Noxet/LEDROCK/firmware/src/http_server.cpp

#include "http_server.h"
#include "freertos/projdefs.h"
#include "message.h"

#include <esp_wifi.h>
#include <esp_event.h>
#include <esp_log.h>
#include <esp_system.h>
#include <nvs_flash.h>
#include <sys/param.h>
#include "core/log.h"
#include "esp_netif.h"
#include "esp_eth.h"
#include "esp_timer.h"
#include "freertos/idf_additions.h"
#include "portmacro.h"
#include "protocol_examples_common.h"
#include "protocol_examples_utils.h"

#include <esp_http_server.h>
#include <vector>
#include <string>


static void disconnect_handler(void* arg, esp_event_base_t event_base, int32_t event_id, void* event_data);
static void connect_handler(void* arg, esp_event_base_t event_base, int32_t event_id, void* event_data);
static esp_err_t startPageHandler(httpd_req_t *req);
static esp_err_t ws_handler(httpd_req_t *req);
static std::vector<std::string> splitPayload(char *msg);
static MsgType parseMsgType(std::string &s);


// Embedded zipped html file
extern const uint8_t index_html_gz_start[] asm("_binary_index_html_gz_start");
extern const uint8_t index_html_gz_end[] asm("_binary_index_html_gz_end");
static size_t index_html_gz_len = index_html_gz_end - index_html_gz_start;

#define MAX_CLIENT_FAILED 5

struct client
{
    int fd;
    int failedAttempts;
};

static std::vector<struct client> g_clients;

/* A simple example that demonstrates using websocket echo server
 */
static const char *TAG = "ws_echo_server";

/*
 * Structure holding server handle
 * and internal socket fd in order
 * to use out of request send
 */
struct async_resp_arg {
    httpd_handle_t hd;
    int fd;
};


HTTPServer::HTTPServer(QueueHandle_t lcQueue)
    : m_lcQueue(lcQueue)
{
    m_httpQueue = xQueueCreate(20, sizeof(char *));
}


void HTTPServer::init()
{
    ESP_ERROR_CHECK(nvs_flash_init());
    ESP_ERROR_CHECK(esp_netif_init());
    ESP_ERROR_CHECK(esp_event_loop_create_default());

    /* This helper function configures Wi-Fi or Ethernet, as selected in menuconfig.
     * Read "Establishing Wi-Fi or Ethernet Connection" section in
     * examples/protocols/README.md for more information about this function.
     */
    ESP_ERROR_CHECK(example_connect());

    /* Register event handlers to stop the server when Wi-Fi or Ethernet is disconnected,
     * and re-start it upon connection.
     */
    ESP_ERROR_CHECK(esp_event_handler_register(IP_EVENT, IP_EVENT_STA_GOT_IP, &connect_handler, this));
    ESP_ERROR_CHECK(esp_event_handler_register(WIFI_EVENT, WIFI_EVENT_STA_DISCONNECTED, &disconnect_handler, this));

    /* Start the server for the first time */
    startWebserver();
}


void HTTPServer::run()
{
    // TODO(noxet): free ptr?
    char *msg = nullptr;
    while(1)
    {
        // Blocking call, wait for message to log
        xQueueReceive(m_httpQueue, &msg, portMAX_DELAY);
        httpd_ws_frame_t ws_pkt;
        memset(&ws_pkt, 0, sizeof(httpd_ws_frame_t));
        ws_pkt.type = HTTPD_WS_TYPE_TEXT;
        ws_pkt.len = strlen(msg);
        ws_pkt.payload = (uint8_t *) msg;

        for (auto it = g_clients.begin(); it != g_clients.end();)
        {
            // TODO(noxet): Send sync instead?
            int ret = httpd_ws_send_frame_async(m_server, it->fd, &ws_pkt);
            if (ret != ESP_OK)
            {
                ESP_LOGI(TAG, "Failed to send log to client fd: %d", it->fd);
                it->failedAttempts++;
            }

            if (it->failedAttempts >= MAX_CLIENT_FAILED)
            {
                // Client probably disconnected, remove them from the list
                it = g_clients.erase(it);
            }
            else
            {
                ++it;
            }
        }
        vTaskDelay(500);
    }
}


httpd_handle_t HTTPServer::getServer()
{
    return m_server;
}


QueueHandle_t HTTPServer::getQueue()
{
    return m_httpQueue;
}


bool HTTPServer::queueLCEvent(Event &e)
{
    return xQueueSend(m_lcQueue, &e, 10);
}


void HTTPServer::startWebserver(void)
{
    const httpd_uri_t ws = {
        .uri        = "/ws",
        .method     = HTTP_GET,
        .handler    = ws_handler,
        .user_ctx   = this,
        .is_websocket = true,
        .handle_ws_control_frames = false,
        .supported_subprotocol = nullptr,
    };

    const httpd_uri_t startPage = {
        .uri = "/",
        .method = HTTP_GET,
        .handler = startPageHandler,
        .user_ctx = nullptr,
        .is_websocket = false,
        .handle_ws_control_frames = false,
        .supported_subprotocol = nullptr,
    };

    httpd_config_t config = HTTPD_DEFAULT_CONFIG();

    // Start the httpd server
    ESP_LOGI(TAG, "Starting server on port: '%d'", config.server_port);
    if (httpd_start(&m_server, &config) == ESP_OK) {
        // Registering the ws handler
        ESP_LOGI(TAG, "Registering URI handlers");
        httpd_register_uri_handler(m_server, &ws);
        httpd_register_uri_handler(m_server, &startPage);
    }

    ESP_LOGI(TAG, "Error starting server!");
}


void HTTPServer::stopWebserver()
{
    if (!m_server) return;

    esp_err_t res = httpd_stop(m_server);
    if (res == ESP_OK)
    {
        LRLOGI("HTTP Server stopped");
    }
    else
    {
        LRLOGI("Failed to stop HTTP Server");
    }
}


/*
 * async send function, which we put into the httpd work queue
 */
static void ws_async_send(void *arg)
{
    static const char * data = "Async data";
    struct async_resp_arg *resp_arg = static_cast<struct async_resp_arg *>(arg);
    httpd_handle_t hd = resp_arg->hd;
    int fd = resp_arg->fd;
    httpd_ws_frame_t ws_pkt;
    memset(&ws_pkt, 0, sizeof(httpd_ws_frame_t));
    ws_pkt.payload = (uint8_t*)data;
    ws_pkt.len = strlen(data);
    ws_pkt.type = HTTPD_WS_TYPE_TEXT;

    httpd_ws_send_frame_async(hd, fd, &ws_pkt);
    free(resp_arg);
}

static esp_err_t trigger_async_send(httpd_handle_t handle, httpd_req_t *req)
{
    struct async_resp_arg *resp_arg = static_cast<struct async_resp_arg *>(malloc(sizeof(struct async_resp_arg)));
    if (resp_arg == NULL) {
        return ESP_ERR_NO_MEM;
    }
    resp_arg->hd = req->handle;
    resp_arg->fd = httpd_req_to_sockfd(req);
    esp_err_t ret = httpd_queue_work(handle, ws_async_send, resp_arg);
    if (ret != ESP_OK) {
        free(resp_arg);
    }
    return ret;
}

static esp_err_t startPageHandler(httpd_req_t *req)
{
    if (req->method == HTTP_GET)
    {
        ESP_LOGI(TAG, "Got GET req");
    }

    char *buf;
    size_t bufLen = httpd_req_get_hdr_value_len(req, "Host") + 1;
    if (bufLen > 1)
    {
        buf = (char *) malloc(bufLen);
        assert(buf);
        ESP_LOGI(TAG, "Allocated %zu bytes for header", bufLen);
        if (httpd_req_get_hdr_value_str(req, "Host", buf, bufLen) == ESP_OK)
        {
            ESP_LOGI(TAG, "Got header -> Host: %s", buf);
        }
        free(buf);
    }

    bufLen = httpd_req_get_url_query_len(req) + 1;
    char decParam[1024]{};
    if (bufLen > 0)
    {
        buf = (char *) malloc(bufLen);
        assert(buf);
        if (httpd_req_get_url_query_str(req, buf, bufLen) == ESP_OK)
        {
            char param[1024];

            if (httpd_query_key_value(buf, "msg", param, sizeof(param)) == ESP_OK)
            {
                ESP_LOGI(TAG, "Got query -> msg: %s", param);
                example_uri_decode(decParam, param, strnlen(param, 1024));
                ESP_LOGI(TAG, "Decoded -> msg: %s", decParam);
            }
        }
        free(buf);
    }

    httpd_resp_set_type(req, "text/html");
    httpd_resp_set_hdr(req, "Content-Encoding", "gzip");

    httpd_resp_send(req, (const char *) index_html_gz_start, index_html_gz_len);

    return ESP_OK;
}

/*
 * This handler echos back the received ws data
 * and triggers an async send if certain message received
 */
static esp_err_t ws_handler(httpd_req_t *req)
{
    HTTPServer *httpServer = static_cast<HTTPServer *>(req->user_ctx);

    if (req->method == HTTP_GET) {
        int client_fd = httpd_req_to_sockfd(req);
        g_clients.push_back({.fd = client_fd, .failedAttempts = 0});
        ESP_LOGI(TAG, "Handshake done, the new connection was opened");
        return ESP_OK;
    }
    ESP_LOGI(TAG, "request method: %d", req->method);
    httpd_ws_frame_t ws_pkt;
    uint8_t *buf = NULL;
    memset(&ws_pkt, 0, sizeof(httpd_ws_frame_t));
    ws_pkt.type = HTTPD_WS_TYPE_TEXT;
    /* Set max_len = 0 to get the frame len */
    esp_err_t ret = httpd_ws_recv_frame(req, &ws_pkt, 0);
    if (ret != ESP_OK) {
        ESP_LOGE(TAG, "httpd_ws_recv_frame failed to get frame len with %d", ret);
        return ret;
    }

    if (ws_pkt.len) {
        /* ws_pkt.len + 1 is for NULL termination as we are expecting a string */
        buf = static_cast<uint8_t *>(calloc(1, ws_pkt.len + 1));
        if (buf == NULL) {
            ESP_LOGE(TAG, "Failed to calloc memory for buf");
            return ESP_ERR_NO_MEM;
        }
        ws_pkt.payload = buf;
        /* Set max_len = ws_pkt.len to get the frame payload */
        ret = httpd_ws_recv_frame(req, &ws_pkt, ws_pkt.len);
        if (ret != ESP_OK) {
            ESP_LOGE(TAG, "httpd_ws_recv_frame failed with %d", ret);
            free(buf);
            return ret;
        }
        ESP_LOGI(TAG, "Got packet with message: %s", ws_pkt.payload);

        // parsing colors and mode
        // format: <MODE>:<COLOR>:?<COLOR>:?<TIME>
        std::vector<std::string> tokens = splitPayload((char *) ws_pkt.payload);
        if (tokens.size() < 2)
        {
            LRLOGI("Not enough arguments");
        };

        // Parse the raw data and turn it into an event for the LED controller
        Event ev;
        ev.type = parseMsgType(tokens.at(0));
        switch (ev.type)
        {
            case MsgType::STATIC:
                ev.data.staticColor.color = Color(tokens.at(1)).rgb;
                break;
            case MsgType::FADE:
                if (tokens.size() < 4)
                {
                    LRLOGI("Not enough arguments for fade color");
                    return ESP_OK;
                }
                ev.data.fadeColor.from = Color(tokens.at(1)).rgb;
                ev.data.fadeColor.to = Color(tokens.at(2)).rgb;
                ev.data.fadeColor.time = std::stoul(tokens.at(3));
                break;
            case MsgType::PULSE:
                if (tokens.size() < 4)
                {
                    LRLOGI("Not enough arguments for pulse color");
                    return ESP_OK;
                }
                ev.data.fadeColor.from = Color(tokens.at(1)).rgb;
                ev.data.fadeColor.to = Color(tokens.at(2)).rgb;
                ev.data.fadeColor.time = std::stoul(tokens.at(3));
                break;
            case MsgType::NONE:
                LRLOGI("NONE type found");
                break;
        }

        if (httpServer->queueLCEvent(ev) != pdPASS)
        {
            LRLOGI("Failed to queue LC event");
        }
    }

    if (ws_pkt.type == HTTPD_WS_TYPE_TEXT &&
        strcmp((char*)ws_pkt.payload,"Trigger async") == 0) {
        free(buf);
        return trigger_async_send(req->handle, req);
    }

    ret = httpd_ws_send_frame(req, &ws_pkt);
    if (ret != ESP_OK) {
        ESP_LOGE(TAG, "httpd_ws_send_frame failed with %d", ret);
    }
    free(buf);
    return ret;
}


static MsgType parseMsgType(std::string &s)
{
    if (s == "static") return MsgType::STATIC;
    if (s == "fade") return MsgType::FADE;
    if (s == "pulse") return MsgType::PULSE;
    return MsgType::NONE;
}


static std::vector<std::string> splitPayload(char *msg)
{
    std::string payload = msg;
    std::vector<std::string> tokens;
    size_t pos = 0;
    while ((pos = payload.find(":")) != std::string::npos)
    {
        std::string token = payload.substr(0, pos);
        tokens.push_back(token);
        payload.erase(0, pos + 1); // erase up to, including, the delimiter
    }
    tokens.push_back(payload);

    return tokens;
}


static void disconnect_handler(void* arg, esp_event_base_t event_base,
                               int32_t event_id, void* event_data)
{
    HTTPServer *http = static_cast<HTTPServer *>(arg);
    http->stopWebserver();
}


static void connect_handler(void* arg, esp_event_base_t event_base,
                            int32_t event_id, void* event_data)
{
    HTTPServer *http = static_cast<HTTPServer *>(arg);
    if (http->getServer() == nullptr) {
        ESP_LOGI(TAG, "Starting webserver");
        http->startWebserver();
    }
}


void HTTPServer::httpServerTask(void *pvParam)
{
    assert(pvParam);
    HTTPServer *hs = static_cast<HTTPServer *>(pvParam);
    hs->init();
    hs->run();
}
