Noxet/LEDROCK/firmware/src/drivers/ledstrip.cpp

#include "ledstrip.h"
#include "core/sys.h"
#include "driver/ledc.h"

#include "esp_log.h"
#include "esp_timer.h"
#include "freertos/idf_additions.h"
#include "freertos/projdefs.h"
#include "hal/ledc_types.h"
#include "portmacro.h"
#include "freertos/semphr.h"


constexpr int GPIO_R = 3;
constexpr int GPIO_G = 4;
constexpr int GPIO_B = 5;

constexpr uint32_t LED_COLOR_SCALE = 32;


Ledstrip::Ledstrip()
{
    m_ledConfig.r = {
        .gpio_num = GPIO_R,
        .speed_mode = LEDC_LOW_SPEED_MODE,
        .channel = LEDC_CHANNEL_0,
        .intr_type = LEDC_INTR_DISABLE,
        .timer_sel = LEDC_TIMER_0,
        .duty = 0,
        .hpoint = 0,
        .sleep_mode = LEDC_SLEEP_MODE_NO_ALIVE_NO_PD,
        .flags = { .output_invert = 0 },
    };

    m_ledConfig.g = {
        .gpio_num = GPIO_G,
        .speed_mode = LEDC_LOW_SPEED_MODE,
        .channel = LEDC_CHANNEL_1,
        .intr_type = LEDC_INTR_DISABLE,
        .timer_sel = LEDC_TIMER_1,
        .duty = 0,
        .hpoint = 0,
        .sleep_mode = LEDC_SLEEP_MODE_NO_ALIVE_NO_PD,
        .flags = { .output_invert = 0 },
    };

    m_ledConfig.b = {
        .gpio_num = GPIO_B,
        .speed_mode = LEDC_LOW_SPEED_MODE,
        .channel = LEDC_CHANNEL_2,
        .intr_type = LEDC_INTR_DISABLE,
        .timer_sel = LEDC_TIMER_2,
        .duty = 0,
        .hpoint = 0,
        .sleep_mode = LEDC_SLEEP_MODE_NO_ALIVE_NO_PD,
        .flags = { .output_invert = 0 },
    };

    m_ledSem = xSemaphoreCreateCounting(3, 3);
}


void Ledstrip::init()
{
    ledc_timer_t timers[] = {LEDC_TIMER_0, LEDC_TIMER_1, LEDC_TIMER_2};
    ledc_timer_config_t ledc_timer = {
        .speed_mode = LEDC_LOW_SPEED_MODE,
        .duty_resolution = LEDC_TIMER_13_BIT,
        .timer_num = LEDC_TIMER_0,
        .freq_hz = 4000,
        .clk_cfg = LEDC_AUTO_CLK,
        .deconfigure = 0,
    };

    for (auto tim : timers)
    {
        ledc_timer.timer_num = tim;
        ledc_timer_config(&ledc_timer);
    }

    ledc_channel_config(&m_ledConfig.r);
    ledc_channel_config(&m_ledConfig.g);
    ledc_channel_config(&m_ledConfig.b);


    ledc_fade_func_install(0);
    ledc_cbs_t callbacks = {
        .fade_cb = &Ledstrip::ledcFadeEndCB,
    };

    ledc_cb_register(m_ledConfig.r.speed_mode, m_ledConfig.r.channel, &callbacks, m_ledSem);
    ledc_cb_register(m_ledConfig.g.speed_mode, m_ledConfig.g.channel, &callbacks, m_ledSem);
    ledc_cb_register(m_ledConfig.b.speed_mode, m_ledConfig.b.channel, &callbacks, m_ledSem);
}


bool Ledstrip::setStaticColor(const Color &color)
{

    /*
     * If there is any fade currently running, we can not set any new fade or static color
     * until the hw fade has completed. Therefore, we need to check the semaphore, if all
     * fades (RGB) has finished before attempting to set any new color.
    */
    if (uxSemaphoreGetCount(m_ledSem) < 2) return false;
    ledc_set_duty(m_ledConfig.r.speed_mode, m_ledConfig.r.channel, color.rgb.r * LED_COLOR_SCALE);
    ledc_set_duty(m_ledConfig.g.speed_mode, m_ledConfig.g.channel, color.rgb.g * LED_COLOR_SCALE);
    ledc_set_duty(m_ledConfig.b.speed_mode, m_ledConfig.b.channel, color.rgb.b * LED_COLOR_SCALE);
    ledc_update_duty(m_ledConfig.r.speed_mode, m_ledConfig.r.channel);
    ledc_update_duty(m_ledConfig.g.speed_mode, m_ledConfig.g.channel);
    ledc_update_duty(m_ledConfig.b.speed_mode, m_ledConfig.b.channel);
    return true;
}


bool Ledstrip::setFadeColor(const Color &from, const Color &to, uint32_t time)
{
    // printf("[%lld ms] sem count: %d\n", esp_timer_get_time() / 1000, uxSemaphoreGetCount(m_ledSem));
    if (uxSemaphoreGetCount(m_ledSem) < 2) return false;
    for (int i = 0; i < 3; i++) xQueueSemaphoreTake(m_ledSem, portMAX_DELAY);

    ledc_set_fade_time_and_start(m_ledConfig.r.speed_mode, m_ledConfig.r.channel, to.rgb.r * LED_COLOR_SCALE, time, LEDC_FADE_NO_WAIT);
    ledc_set_fade_time_and_start(m_ledConfig.g.speed_mode, m_ledConfig.g.channel, to.rgb.g * LED_COLOR_SCALE, time, LEDC_FADE_NO_WAIT);
    ledc_set_fade_time_and_start(m_ledConfig.b.speed_mode, m_ledConfig.b.channel, to.rgb.b * LED_COLOR_SCALE, time, LEDC_FADE_NO_WAIT);
    return true;
}


bool Ledstrip::ledcFadeEndCB(const ledc_cb_param_t *param, void *userArg)
{
    BaseType_t taskAwoken = pdFALSE;

    if (param->event == LEDC_FADE_END_EVT)
    {
        SemaphoreHandle_t sem = (SemaphoreHandle_t) userArg;
        // ESP_EARLY_LOGW("LC", "[%lld ms] giving sem: %d", getUptime(), uxSemaphoreGetCount(sem));
        xSemaphoreGiveFromISR(sem, &taskAwoken);
    }

    return taskAwoken;
}
