Noxet/LEDROCK/firmware/src/drivers/ledstrip.h

#pragma once

#include "core/color.h"

#include "core/led_driver.h"
#include "freertos/FreeRTOS.h"
#include "freertos/semphr.h"
#include "driver/ledc.h"

class Ledstrip : public ILedDriver
{
public:
    Ledstrip();

    void init() override;
    bool setStaticColor(const Color &color) override;
    bool setFadeColor(const Color &from, const Color &to, uint32_t time) override;

private:

    struct ledcChannels
    {
        ledc_channel_config_t r;
        ledc_channel_config_t g;
        ledc_channel_config_t b;
    };

    ledcChannels m_ledConfig;
    SemaphoreHandle_t m_ledSem;

    // ISR callback
    static bool IRAM_ATTR ledcFadeEndCB(const ledc_cb_param_t *param, void *userArg);
};
